msharp176/LoRa-Water-Quality-Management-System/Sensor Node/pcb layout/models/ABM8-272-T3_ABR.step

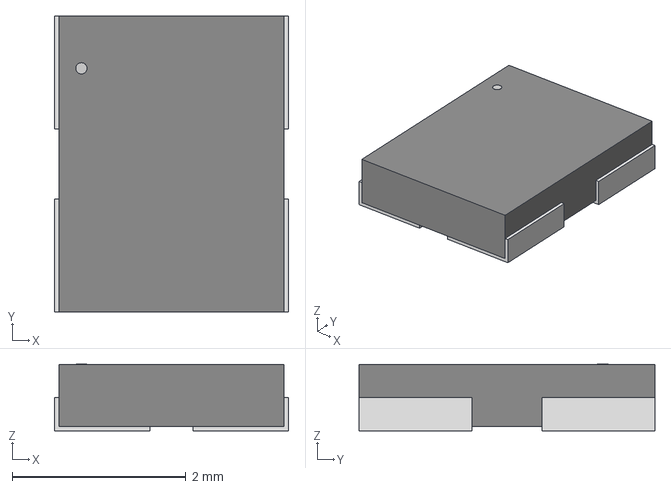
[picture p50: CAD file, 2025-08-04]
Sensor Node/pcb layout/models/ABM8-272-T3_ABR.step
2.69 x 3.40 x 0.765 mm
