msharp176/LoRa-Water-Quality-Management-System/Sensor Node/pcb layout/models/TG2520SMN_32.0000M-MCGNNM0.stp

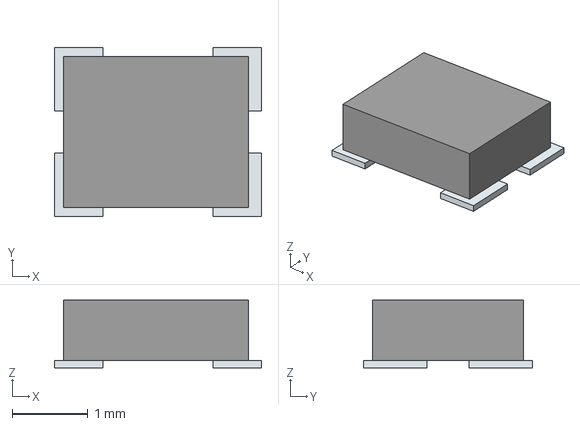
[picture p51: CAD file, 2025-08-01]
Sensor Node/pcb layout/models/TG2520SMN_32.0000M-MCGNNM0.stp
2.74 x 2.24 x 0.9 mm
Pins
