msharp176/LoRa-Water-Quality-Management-System/Sensor Node/pcb layout/models/SX1262IMLTRT.step

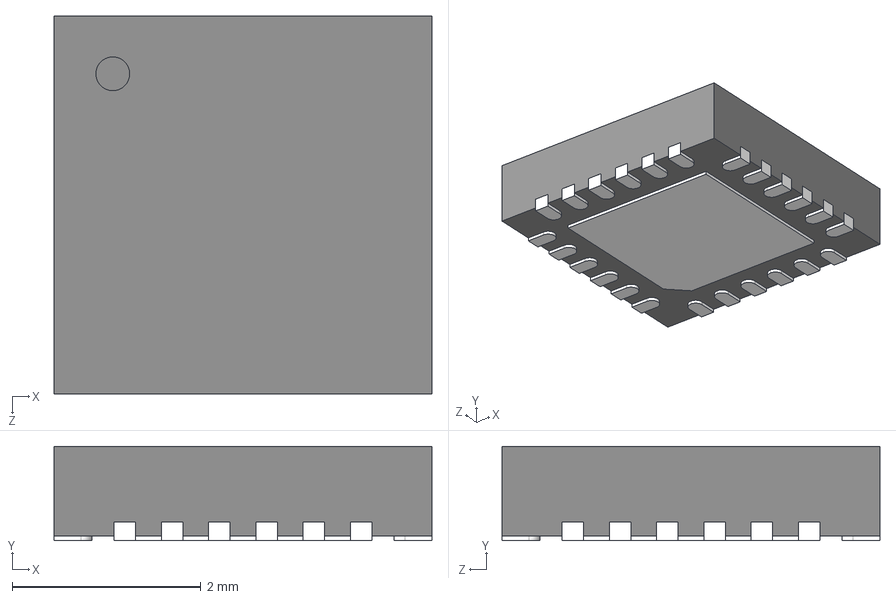
[picture p52: CAD file, 2025-08-01]
Sensor Node/pcb layout/models/SX1262IMLTRT.step
4.00 x 1.00 x 4.00 mm
