msharp176/LoRa-Water-Quality-Management-System/Sensor Node/pcb layout/models/BGS12WN6E6327XTSA1.step

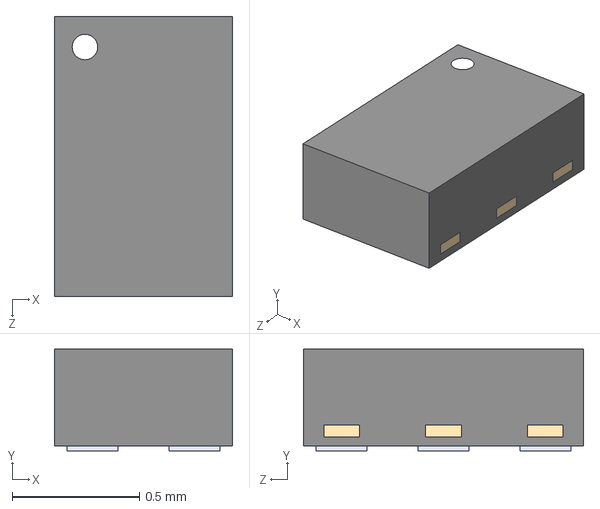
[picture p53: CAD file, 2025-08-01]
Sensor Node/pcb layout/models/BGS12WN6E6327XTSA1.step
0.7 x 0.4 x 1.10 mm
