msharp176/LoRa-Water-Quality-Management-System/Sensor Node/simulation/pH_sensor_preamp/pH_sensor_preamp-PSpiceFiles/SCHEMATIC1/time_domain/time_domain.cir

** Profile: "SCHEMATIC1-time_domain"  [ C:\Users\mshar\Documents\capstone\simulation\pH_sensor_preamp\ph_sensor_preamp-pspicefiles\schematic1\time_domain.sim ] 

** Creating circuit file "time_domain.cir" 
** WARNING: THIS AUTOMATICALLY GENERATED FILE MAY BE OVERWRITTEN BY SUBSEQUENT SIMULATIONS

*Libraries: 
* Profile Libraries :
* Local Libraries :
* From [PSPICE NETLIST] section of C:\cds_spb_home\cdssetup\OrCAD_PSpiceTIPSpice_Install\23.1.0\PSpice.ini file:
.lib "nom_pspti.lib" 
.lib "nom.lib" 

*Analysis directives: 
.TRAN  0 1 0 1m 
.OPTIONS ADVCONV
.OPTIONS FILEMODELSEARCH
.PROBE64 V(alias(*)) I(alias(*)) W(alias(*)) D(alias(*)) NOISE(alias(*)) 
.INC "..\SCHEMATIC1.net" 


.END
