msharp176/LoRa-Water-Quality-Management-System/Sensor Node/simulation/Software-Defined Instrumentation Amplifier/Software_Defined_Instrumentation_Amplifier/Software_Defined_Instrumentation_Amplifier-PSpiceFiles/SCHEMATIC1/bias_point/bias_point.cir

** Profile: "SCHEMATIC1-bias_point"  [ c:\users\mshar\documents\capstone\simulation\software-defined instrumentation amplifier\software_defined_instrumentation_amplifier\software_defined_instrumentation_amplifier-pspicefiles\schematic1\bias_point.sim ] 

** Creating circuit file "bias_point.cir" 
** WARNING: THIS AUTOMATICALLY GENERATED FILE MAY BE OVERWRITTEN BY SUBSEQUENT SIMULATIONS

*Libraries: 
* Profile Libraries :
* Local Libraries :
* From [PSPICE NETLIST] section of C:\cds_spb_home\cdssetup\OrCAD_PSpiceTIPSpice_Install\23.1.0\PSpice.ini file:
.lib "nom_pspti.lib" 
.lib "nom.lib" 

*Analysis directives: 
.OPTIONS ADVCONV
.OPTIONS FILEMODELSEARCH
.PROBE64 V(alias(*)) I(alias(*)) W(alias(*)) D(alias(*)) NOISE(alias(*)) 
.INC "..\SCHEMATIC1.net" 


.END
