msharp176/LoRa-Water-Quality-Management-System/Sensor Node/simulation/Draft1.asc

R1: res; 10k
R2: res; 10k
R3: res; 10k
R4: res; 10k
R5: res; 10k
R6: res; 10k
R7: res; 10k
U2: UniversalOpAmp2
U3: UniversalOpAmp2
U4: UniversalOpAmp2
V1: voltage; 5
V2: voltage; 1
V3: voltage; 0
Named nets: 0, Vdd, Vo, V2, V1
.op
