msharp176/LoRa-Water-Quality-Management-System/Sensor Node/simulation/SensorOffsetAmplifier.asc

R1: res; 10k
R2: res; 10k
R3: res; 10k
R4: res; 10k
U1: UniversalOpAmp2
V1: voltage; 2
V2: voltage; 3
V3: voltage; 0.2
V4: voltage; 15
V5: voltage; 15
Named nets: 0, Vin, V+, V-, VDD, VSS, Vout
.op
Vout = Vin + V+ - V-
 
easy peasy.
