msharp176/LoRa-Water-Quality-Management-System/Sensor Node/simulation/turbiditySensor.asc

D1: zener; zener3
R1: res; 3.6k
R2: res; 10k
R3: res; 45k
R4: res; 45k
R5: res; 1k
R6: res; 1k
R7: res; 8k
R8: res; 8k
R9: res; 1.3k
R10: res; 10k
U1: UniversalOpAmp2
U2: UniversalOpAmp2
U3: UniversalOpAmp2
V1: voltage; 5
V2: voltage; PWL file=C:\Users\mshar\Documents\capstone\simulation\turb_sensor.txt
Named nets: Vcc, 0, Vout, Vsensor, Vref
.tran 0 0.1s 0 0.001ms
.model zener3 D(Vrev=3 type=zener)
