msharp176/LoRa-Water-Quality-Management-System/Sensor Node/code/sys_utils/headers/hardware.h

/******************************************************************************************************************** 
*   
*   @file hardware.h
*
*   @brief Global Hardware Context Types and Definitions for the LoRa Water Quality Management System Sensor Node Firmware
*
*   @author Matthew Sharp
*   
*   @remark Penn State Harrisburg Electrical Engineering Senior Capstone Design Course, Fall 2025
*
*********************************************************************************************************************/

#ifndef HARDWARE_H
#define HARDWARE_H

#include "pico/stdlib.h"
#include "hardware/spi.h"
#include "hardware/i2c.h"
#include "hardware/powman.h"


//----------------------------------------------------------------------------------------------------------------------------------------------------------------------
// C Standard Library Includes



//----------------------------------------------------------------------------------------------------------------------------------------------------------------------

//----------------------------------------------------------------------------------------------------------------------------------------------------------------------
// Project Includes


//----------------------------------------------------------------------------------------------------------------------------------------------------------------------

//----------------------------------------------------------------------------------------------------------------------------------------------------------------------
// Global Definitions & Aliases

#define SPI0_MOSI GP19
#define SPI0_MISO GP16
#define SPI0_SCK GP18

#define EN_5V GP2
#define STATUS_LED GP3
#define TX_LED GP4
#define RX_LED GP5
#define ERR_LED GP6

#pragma region GPIO Aliases

#define GPIO_LOW 0
#define GPIO_HIGH 1

#define GP0 0
#define GP1 1
#define GP2 2
#define GP3 3
#define GP4 4
#define GP5 5
#define GP6 6
#define GP7 7
#define GP8 8
#define GP9 9
#define GP10 10
#define GP11 11
#define GP12 12
#define GP13 13
#define GP14 14
#define GP15 15
#define GP16 16
#define GP17 17
#define GP18 18
#define GP19 19
#define GP20 20
#define GP21 21
#define GP22 22
#define GP23 23
#define GP24 24
#define GP25 25
#define GP26 26
#define GP27 27
#define GP28 28

#pragma endregion

#define SPI_FREQ_GLOBAL 10000000 // 10 MHz
#define COMMS_RETRIES 5

#define RADIO_TIMEOUT_GLOBAL_US 10000 // 10 ms

#define QTY_GPIO_PINS NUM_BANK0_GPIOS

#define MCU_POWMAN_NOVO_ELEMENTS 8

//----------------------------------------------------------------------------------------------------------------------------------------------------------------------


//----------------------------------------------------------------------------------------------------------------------------------------------------------------------
// Interface Types

/**
 * 
 * @brief Struct containing all data necessary to define a single SPI instance within the HAL
 * 
 */
typedef struct spi_context_s {
    spi_inst_t* inst;
    uint8_t     mosi;
    uint8_t     miso;
    uint8_t     sck;
    uint32_t    baud;
    uint8_t     xfer_bits;
    uint8_t     polarity;
    uint8_t     phase;
    uint8_t     lsb_msb_first;
} spi_context_t;

/**
 * 
 * @brief Struct containing all data necessary to define a single I2C instance within the HAL.
 * 
 */
typedef struct i2c_context_s {
    i2c_inst_t* inst;
    uint        sda;
    uint        scl;
    uint        baud;
} i2c_context_t;

/**
 * @brief GPIO driven IRQ configuration data
 */
typedef struct gpio_driven_irq_context_s {
    uint8_t pin;
    uint32_t source_mask;
    void * callback;
} gpio_driven_irq_context_t;

/**
 * @brief A handler for a GPIO-driven interrupt
 */
typedef void (*gpio_isr_handler_t)(gpio_driven_irq_context_t*);  // A function pointer to a GPIO ISR handler that accepts a pointer to an IRQ context type as its input.


//----------------------------------------------------------------------------------------------------------------------------------------------------------------------

//----------------------------------------------------------------------------------------------------------------------------------------------------------------------
// Hardware Types

/**
 * @brief sx126x Radio Configuration Data
 */
typedef struct sx126x_context_s {
    const gpio_driven_irq_context_t * irq_context;    // The interrupt event trigger of the module.
    const spi_context_t* spi_context;                 // The SPI bus of the radio module
    const uint8_t        rst;                         // Reset - Pull LOW for 100us to initiate a reset.
    const uint8_t        busy;                        // Busy Indicator - HIGH indicates that sx126x is busy and can not be written to
    const uint32_t       radio_operation_timeout_us;  // Timeout to wait for radio to leave busy state
    const uint8_t        cs;                          // Chip select GPIO Pin.
    const char *         designator;                  // Radio designator string
    const uint8_t        tx_buf_start;
    const uint8_t        rx_buf_start;
} sx126x_context_t;

/**
 * @brief mcp4651 Digital Potentiometer Configuration Data
 */
typedef struct mcp4651_context_s {
    const i2c_context_t* i2c_context;   // The i2c context where the digipot lives
    const uint8_t addr;                 // I2C address
    double base_resistance_a;   // The full-width resistance of POT A
    double base_resistance_b;   // The full-width resistance of POT B
    uint16_t wiper_position_a;          // The current tap position of wiper A
    uint16_t wiper_position_b;          // The current tap position of wiper B
    uint16_t total_steps;               // The number of available tap positions
    double resistance_per_step;         // The resistance per step (Rs) of the device
} mcp4651_context_t;

/**
 * @brief mcp3425 16-Bit A-D Converter Configuration Data
 */

typedef struct mcp3425_context_s {
    const i2c_context_t* i2c_context;
    const uint8_t addr;
    uint8_t gain;
    uint8_t sampling_rate;
    bool continuous_conversion_mode_enabled;
} mcp3425_context_t;

/**
 * @brief mxl23l3233f Serial NOR Flash Configuration Data
 */
typedef struct mxl23l3233f_context_s {
    const spi_context_t* spi_context;   // The SPI context where the flash chip lives
    const uint8_t cs;                   // Chip Select Pin
    const uint32_t size;                // Size of the flash memory, in bytes.
    const uint32_t sectors;             // Number of 4kB sectors
    const uint32_t blocks_32kB;         // Number of 32kB blocks
    const uint32_t blocks_64kB;         // Number of 64kB blocks
} mxl23l3233f_context_t;

typedef struct tmux1309_context_s {
    const uint8_t enable;               // Enable Pin (active low)
    const uint8_t sel0;                 // Select 0 Pin
    const uint8_t sel1;                 // Select 1 Pin
} tmux1309_context_t;

/**
 * @brief Error Sources for the LoRa Water Quality Management System
 */
typedef enum lwqms_errs_e {
    ERR_SPI_TRANSACTION_FAIL = 0,
    ERR_BAD_CRC = 1,
    ERR_LORA_TIMEOUT = 2,
    ERR_ARGUMENT = 3,
    ERR_BAD_SETUP = 4,
    ERR_I2C_TRANSACTION_FAIL = 5,
    ERR_POST_FAIL = 6,
    ERR_LORA_FAIL = 7,
    ERR_RDT3_0 = 8
} lwqms_errs_t;

/**
 * @brief Error Logging Levels for the LoRa Water Quality Management System
 */
typedef enum lwqms_err_severity_e {
    ERR_SEV_FATAL = 0,
    ERR_SEV_REBOOT = 1,
    ERR_SEV_NONFATAL = 2
} lwqms_err_severity_t;

// Hardware contexts used to interface with the Software-Defined Instrumentation Amplifier
typedef struct sdia_context_s {
    mcp4651_context_t *context_digipot_gain;
    mcp4651_context_t *context_digipot_dc_offset;
    mcp4651_context_t *context_digipot_output_reference;
    mcp3425_context_t *context_adc;
    tmux1309_context_t *context_mux;
} sdia_context_t;

/**
 * @brief Exposes domain-wise power management configuration for the RP2350
 */
typedef union rp2350_power_mgmt_setting_u {
    struct domains_s {
        bool swcore_enable, xip_enable, sram0_enable, sram1_enable;
    } domains;
    bool as_arr[4]; // Overlays the domain fields as a list of booleans.
} rp2350_power_mgmt_setting_t;

/**
 * @brief Provides hardware-specific configuration data for RP2350 power management.
 */
typedef struct rp2350_power_state_context_s {
    powman_power_state active_power_state;
    powman_power_state dormant_power_state;
} rp2350_power_state_context_t;

//----------------------------------------------------------------------------------------------------------------------------------------------------------------------

//----------------------------------------------------------------------------------------------------------------------------------------------------------------------
// Interface References

extern spi_context_t context_spi_0;

extern i2c_context_t context_i2c_0;

extern i2c_context_t context_i2c_1;

const extern gpio_driven_irq_context_t irq_context_radio_0;

//----------------------------------------------------------------------------------------------------------------------------------------------------------------------

//----------------------------------------------------------------------------------------------------------------------------------------------------------------------
// Hardware References

extern sx126x_context_t context_radio_0;

extern uint8_t err_led;

extern mcp4651_context_t context_digipot_offset;

extern mcp4651_context_t context_digipot_gain;

extern mcp4651_context_t context_digipot_reference;

extern mcp3425_context_t context_adc_0;

extern mxl23l3233f_context_t context_flash_0;

extern tmux1309_context_t context_mux_0;

extern sdia_context_t context_sdia_0;

extern rp2350_power_mgmt_setting_t power_mgmt_dormant_state;

//----------------------------------------------------------------------------------------------------------------------------------------------------------------------


#endif

/* --- EOF ------------------------------------------------------------------ */
